pertbanking/led-cube/pi/src/LEDCube.cpp

/*
 * Software License Agreement:
 * do whatever teh crap you want with this software
 * just mention my name if you use it, bitte
 *
 * Author: Joshua Petrin <joshua.m.petrin@vanderbilt.edu>
 */

#ifndef LEDCUBE_CPP_
#define LEDCUBE_CPP_

#include "LEDCube.h"

#include <condition_variable>
#include <iostream>
#include <memory>
#include <mutex>
#include <thread>
#include <vector>
#include <cmath>
#include <cassert>
#include <cstdint>
#include <cstdio>

#include <serial/serial.h>


using namespace std;

// comment out to squelch debug messages to the console.
// #define CUBE_DEBUG


// ==================================
// constants, (con/de)structors, copiers, and instances
// ==================================


LEDCube::LEDCube(int framerate)
    : framerate(framerate)
    , data(
        vector<vector<vector<bool>>>(
            CUBE_SIZE, vector<vector<bool>>(
                CUBE_SIZE, vector<bool>(
                    CUBE_SIZE, false)
                )
            )
        )
    , data_current(true)
    , cube_pass(
        vector<vector<uint8_t>>(
                CUBE_SIZE, 
                vector<uint8_t>(CUBE_SIZE, 0)
            )
        )
    , render_thread()
    , data_m()
    , data_lock(this->data_m, std::defer_lock)
    , broadcast_lock(this->data_m, std::defer_lock) {}


// =======================================
// timing and I/O control
// =======================================

void LEDCube::broadcastLock() {
    this->broadcast_lock.lock();
}

void LEDCube::broadcastUnlock() {
    if (this->broadcast_lock.owns_lock())
        this->broadcast_lock.unlock();
}

void LEDCube::setMessageRate(int f) {
    this->framerate = f;
}

int LEDCube::getMessageRate() const {
    return this->framerate;
}

void LEDCube::lock() {
    this->data_lock.lock();
}

void LEDCube::unlock() {
    this->data_lock.unlock();
}



// ===============================================
// data management functions
// ===============================================

vector<vector<vector<bool>>>& LEDCube::getCube() {
    return this->data;
}

const vector<vector<uint8_t>>& LEDCube::getCubeData() {
    if (!(this->data_current)) {
        // clear the data for the cube
        this->cube_pass = vector<vector<uint8_t>>(
            CUBE_SIZE, vector<uint8_t>(CUBE_SIZE, 0)
        );

        // convert the cube bool into the proper x,y,z uint8_t array
        for (int i = 0; i < CUBE_SIZE; ++i) {
            for (int j = 0; j < CUBE_SIZE; ++j) {
                for (int k = 0; k < CUBE_SIZE; ++k) {
                    this->cube_pass[k][j] += this->data[i][j][k] << i;
                }
            }
        }
    }

    #ifdef CUBE_DEBUG
    for (int i = CUBE_SIZE-1; i >= 0; --i) {
        for (int j = 0; j < CUBE_SIZE; ++j) {
            printf(" %X", cube_pass[i][j]);
        }
        printf("\n");
    }
    printf("\n");
    #endif

    return this->cube_pass;
}



// ==========================================
// pixel manipulation functions
// ==========================================

void LEDCube::clear() {
    // don't forget this!
    this->data_current = false;

    this->data = vector<vector<vector<bool>>>(
        CUBE_SIZE, vector<vector<bool>>(
            CUBE_SIZE, vector<bool>(
                CUBE_SIZE, false)
            )
        );
}

void LEDCube::setVoxel(uint8_t x, uint8_t y, uint8_t z, bool on) {
    // don't forget this!
    this->data_current = false;

    this->data[x][y][z] = on;
}

void LEDCube::setVoxel(float x, float y, float z, bool on, float scale) {
    // don't forget this!
    this->data_current = false;

    this->data[int(x/scale + 0.5)][int(y/scale + 0.5)][int(z/scale + 0.5)] = on;
}

void LEDCube::voxelOn(uint8_t x, uint8_t y, uint8_t z) {
    this->setVoxel(x, y, z, true);
}

void LEDCube::voxelOn(float x, float y, float z, float scale) {
    this->setVoxel(x, y, z, true, scale);
}

void LEDCube::voxelOff(uint8_t x, uint8_t y, uint8_t z) {
    this->setVoxel(x, y, z, false);
}

void LEDCube::voxelOff(float x, float y, float z, float scale) {
    this->setVoxel(x, y, z, false, scale);
}

bool LEDCube::getVoxel(uint8_t x, uint8_t y, uint8_t z) const {
    return this->data[x][y][z];
}

void LEDCube::drawLine(
    float x0,
    float y0,
    float z0,
    float x1,
    float y1,
    float z1,
    float scale) {

    if (scale != 1.0) {
        x0 /= scale;
        x1 /= scale;
        y0 /= scale;
        y1 /= scale;
        z0 /= scale;
        z1 /= scale;
    }

    vector< vector<bool> > xyplane(CUBE_SIZE, vector<bool>(CUBE_SIZE, false));
    vector< vector<bool> > xzplane(CUBE_SIZE, vector<bool>(CUBE_SIZE, false));
    vector< vector<bool> > yzplane(CUBE_SIZE, vector<bool>(CUBE_SIZE, false));

    // set (x1,y1,z1) to true
    xyplane[int(x1 + 0.5)][int(y1 + 0.5)] = true;
    xzplane[int(x1 + 0.5)][int(z1 + 0.5)] = true;
    yzplane[int(y1 + 0.5)][int(z1 + 0.5)] = true;

    // goal: traverse each axis and follow the projected line on each plane.
    //       each projected line has a slope. we move in the other axes
    //       proportional to the slope, just like we would a normal line.
    //       if every plane marks a point as true on its respective axis, 
    //       then the point is illuminated.

    float x_prog, y_prog, z_prog;

    if (abs(x0 - x1) > 0.0001) {
        // xy-plane and xz-plane
        y_prog = y0;
        z_prog = z0;
        float xy_slope = (y0 - y1) / (x0 - x1);
        float xz_slope = (z0 - z1) / (x0 - x1);
        for (
          x_prog = x0;
          (x0 < x1)? x_prog < x1 : x_prog > x1;
          x_prog += (x0 < x1)? 1.0 : -1.0) {
            xyplane[int(x_prog + 0.5)][int(y_prog + 0.5)] = true;
            xzplane[int(x_prog + 0.5)][int(z_prog + 0.5)] = true;
            y_prog += (x0 < x1)? xy_slope : -xy_slope;
            z_prog += (x0 < x1)? xz_slope : -xz_slope;
        }
    }

    if (abs(y0 - y1) > 0.0001) {
        // xy-plane and yz-plane
        x_prog = x0;
        z_prog = z0;
        float yx_slope = (x0 - x1) / (y0 - y1);
        float yz_slope = (z0 - z1) / (y0 - y1);
        for (
          y_prog = y0;
          (y0 < y1)? y_prog < y1 : y_prog > y1;
          y_prog += (y0 < y1)? 1.0 : -1.0) {
            xyplane[int(x_prog + 0.5)][int(y_prog + 0.5)] = true;
            yzplane[int(y_prog + 0.5)][int(z_prog + 0.5)] = true;
            x_prog += (y0 < y1)? yx_slope : -yx_slope;
            z_prog += (y0 < y1)? yz_slope : -yz_slope;
        }
    }

    if (abs(z0 - z1) > 0.0001) {
        // xz-plane and yz-plane
        x_prog = x0;
        y_prog = y0;
        float zx_slope = (x0 - x1) / (z0 - z1);
        float zy_slope = (y0 - y1) / (z0 - z1);
        for (
          z_prog = z0;
          (z0 < z1)? z_prog < z1 : z_prog > z1;
          z_prog += (z0 < z1)? 1.0 : -1.0) {
            xzplane[int(x_prog + 0.5)][int(z_prog + 0.5)] = true;
            yzplane[int(y_prog + 0.5)][int(z_prog + 0.5)] = true;
            x_prog += (z0 < z1)? zx_slope : -zx_slope;
            y_prog += (z0 < z1)? zy_slope : -zy_slope;
        }
    }

    // if the planes all agree, illuminate the voxel
    for (uint8_t i = 0; i < CUBE_SIZE; ++i) {
        for (uint8_t j = 0; j < CUBE_SIZE; ++j) {
            if (xyplane[i][j]) {
                for (uint8_t k = 0; k < CUBE_SIZE; ++k) {
                    if (xzplane[i][k] and yzplane[j][k])
                        this->voxelOn(i,j,k);
                }
            }
        }
    }

}

void LEDCube::drawXPlane(uint8_t x) {
    // don't forget this!
    this->data_current = false;

    for (int i = 0; i < CUBE_SIZE; ++i)
        for (int j = 0; j < CUBE_SIZE; ++j)
            data[x][i][j] = true;
}

void LEDCube::drawYPlane(uint8_t y) {
    // don't forget this!
    this->data_current = false;

    for (int i = 0; i < CUBE_SIZE; ++i)
        for (int j = 0; j < CUBE_SIZE; ++j)
            data[i][y][j] = true;
}
    
void LEDCube::drawZPlane(uint8_t z) {
    // don't forget this!
    this->data_current = false;

    for (int i = 0; i < CUBE_SIZE; ++i)
        for (int j = 0; j < CUBE_SIZE; ++j)
            data[i][j][z] = true;
}

void LEDCube::drawBox(
    float x0, 
    float y0, 
    float z0, 
    float x1, 
    float y1, 
    float z1, 
    bool filled,
    float scale) {

    if (scale != 1.0) {
        x0 /= scale;
        x1 /= scale;
        y0 /= scale;
        y1 /= scale;
        z0 /= scale;
        z1 /= scale;
    }

    filled = false;
    if (filled) {
        // TODO: Implement a 'filled' algorithm
    } else {
        // TODO: Do NOT use the drawLine method here. It is inefficient, since
        //       it generalizes to line segments not parallel to the axes.
        this->drawLine(x0, y0, z0, x1, y0, z0);
        this->drawLine(x0, y0, z0, x0, y1, z0);
        this->drawLine(x0, y0, z0, x0, y0, z1);
        this->drawLine(x1, y0, z0, x1, y0, z1);
        this->drawLine(x1, y0, z1, x0, y0, z1);
        this->drawLine(x0, y1, z0, x0, y1, z1);
        this->drawLine(x0, y1, z1, x0, y0, z1);
        this->drawLine(x0, y1, z0, x1, y1, z0);
        this->drawLine(x1, y0, z0, x1, y1, z0);
        this->drawLine(x0, y1, z1, x1, y1, z1);
        this->drawLine(x1, y0, z1, x1, y1, z1);
        this->drawLine(x1, y1, z0, x1, y1, z1);
    }
}


#endif
