pertbanking/led-cube/pi/src/3DViewer.cpp

#include <iostream>
#include <GL/glut.h>


using namespace std;

int cx = 0;
int cy = 0;
int cz = 0;

int cn;

struct Quads {
  int x1;
  int y1;
  int z1;
  
  int x2;
  int y2;
  int z2;

  int x3;
  int y3;
  int z3;

  int x4;
  int y4;
  int z4;

  float r;
  float g;
  float b;

  int state;
  int total;

};

Quads Q[100];


void addQuad() {

  Q[0].state++; 
  
  if (Q[0].state > 4) { Q[0].state = 1; }


  int st = Q[0].state;


  if (st == 1) {

    Q[0].total++;
    cn = Q[0].total;
  }

  if (st == 1) {

    Q[cn].x1 = cx;
    Q[cn].y1 = cy;
    Q[cn].z1 = cz;
  }

  if (st == 1 || st == 2) {

    Q[cn].x2 = cx;
    Q[cn].y2 = cy;
    Q[cn].z2 = cz;

  }

  if (st == 1 || st == 2 || st == 3) {

    Q[cn].x3 = cx;
    Q[cn].y3 = cy;
    Q[cn].z3 = cz;

  }

  if (st == 1 || st == 2 || st == 3 || st == 4) {

    Q[cn].x4 = cx;
    Q[cn].y4 = cy;
    Q[cn].z4 = cz;

  }

}


void drawQuads() {

  int i;
  int addThis = Q[0].total + 1;

  for (i = 1; i < addThis; i++) {
    
    glBegin(GL_QUADS);
    glColor3f(Q[i].r, Q[i].g, Q[i].b);
    glVertex3f(Q[i].x1, Q[i].y1, Q[i].z1);
    glVertex3f(Q[i].x2, Q[i].y2, Q[i].z2);
    glVertex3f(Q[i].x3, Q[i].y3, Q[i].z3);
    glVertex3f(Q[i].x4, Q[i].y4, Q[i].z4);
    glEnd();
  }

}


void theCube() {

  //glColor3f(1, 1, 1);
  //glutSolidCube(0.4);

  glPushMatrix();
  glColor3f(1, 1, 1);
  glTranslatef(cx, cy, cz);
  glutSolidCube(0.4);
  glPopMatrix();

}


void drawGrid() {

  for (int i = 0; i < 40; i++) {

    glPushMatrix();

    if (i < 20) { 

      glTranslatef(0, 0, i); 

    }

    if (i >= 20) { 

      glTranslatef(i - 20, 0, 0);
      glRotatef(-90, 0, 1, 0); 

    }

    glBegin(GL_LINES);
    glColor3f(1, 1, 1); 
    glLineWidth(1);
    glVertex3f(0, -0.1, 0); 
    glVertex3f(19, -0.1, 0);
    glEnd();
    glPopMatrix();
  }

}


void display() {

  glClear(GL_COLOR_BUFFER_BIT | GL_DEPTH_BUFFER_BIT);
  glLoadIdentity();
  glTranslatef(-13, 0, -45);
  glRotatef(40, 1, 1, 0);

  drawGrid();
  drawQuads();
  theCube();
  glutSwapBuffers();
}


void init() {

  glMatrixMode(GL_PROJECTION);
  glLoadIdentity();
  gluPerspective(35, 1.0f, 0.1f, 1000);
  glMatrixMode(GL_MODELVIEW);
  glEnable(GL_DEPTH_TEST);

  //glClearColor(0.1, 0.1, 0.1, 1);
  glClearColor(0.2, 0.2, 0.2, 1);

}

void keyboard(unsigned char key, int x, int y) {

  if (key == 'w') {
    cz -= 1;
  }

  if (key == 's') {
    cz += 1;
  }

  if (key == 'a') {
    cx -= 1;
  }

  if (key == 'd') {
    cx += 1;
  }

  if (key == 'q') {
    cy += 1;
  }

  if (key == 'e') {
    cy -= 1;
  }

  // space bar function
  if (key == 32) {

    addQuad();
  }

  // for colors
  if (key == 'r') {

    Q[cn].r = 1;
    Q[cn].g = 0;
    Q[cn].b = 0;
  }

  if (key == 'g') {

    Q[cn].r = 0;
    Q[cn].g = 1;
    Q[cn].b = 0;
  }

  if (key == 'b') {

    Q[cn].r = 0;
    Q[cn].g = 0;
    Q[cn].b = 1;
  }

  if (key == 'y') {

    Q[cn].r = 1;
    Q[cn].g = 1;
    Q[cn].b = 0;
  }

  glutPostRedisplay();
}

int main(int argc, char **argv) {

  glutInit(&argc, argv);
  glutInitDisplayMode(GLUT_DOUBLE);
  glutInitWindowSize(800, 600);
  glutCreateWindow("Sample Grid Window");
  glutDisplayFunc(display);

  glutKeyboardFunc(keyboard);

  init();

  glutMainLoop();

  return 0;


}


// TODO: Take a look at the gluLookAt function. 
// TODO: The viewing will be controlled by the mouse. You will use spherical 
//       coordinates to determine where the camera sits in the cartesian
//       coordinate axes.
